VirgileBoraud/myo/Photos&Vidéos/photo.jpg

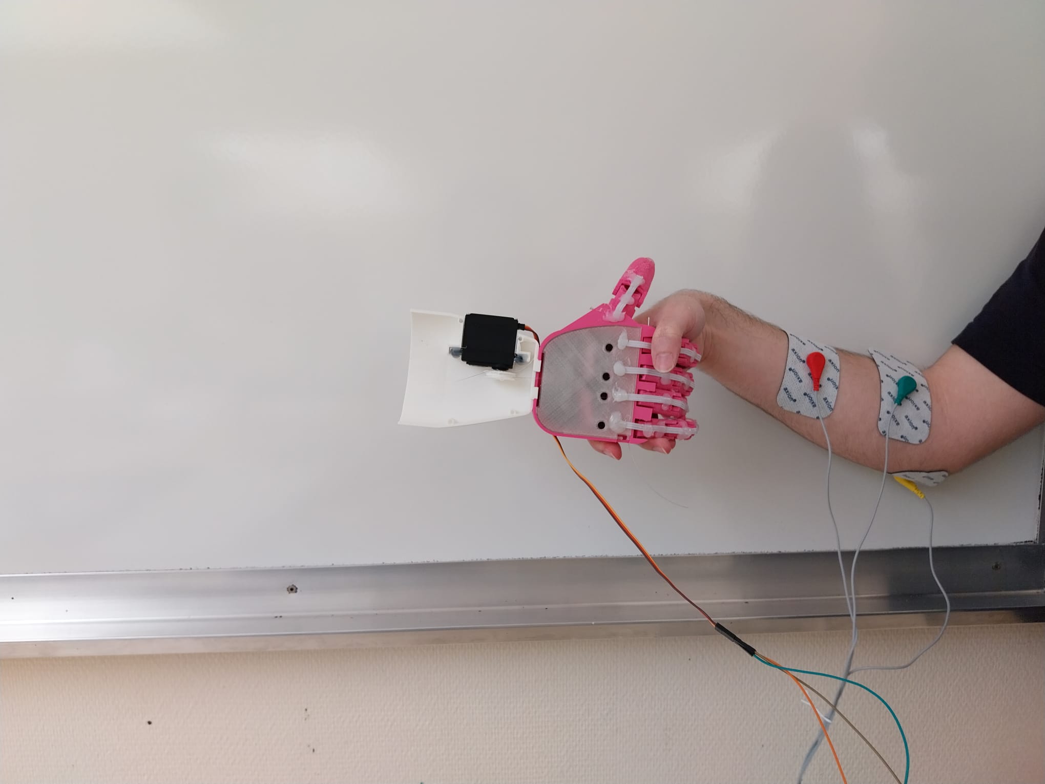
Photos&Vidéos/photo.jpg
