VirgileBoraud/myo/Photos&Vidéos/photo_presentation.jpg

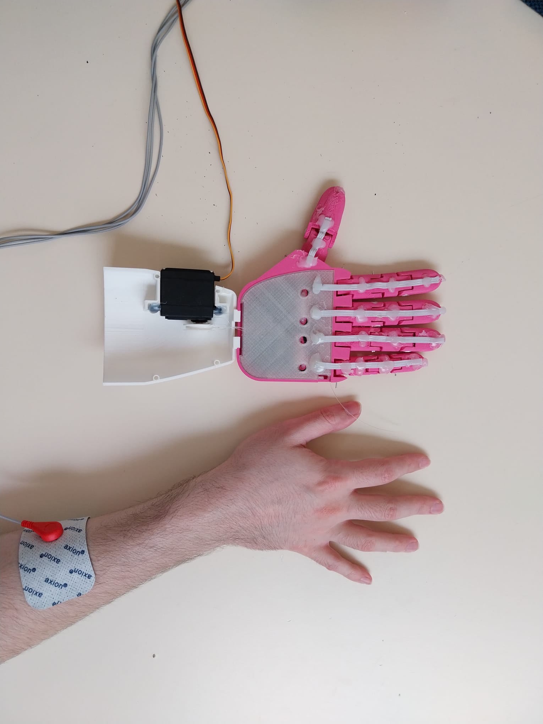
Photos&Vidéos/photo_presentation.jpg
