VirgileBoraud/myo/Programmes/affichage_capteur_EMG/repos.jpg

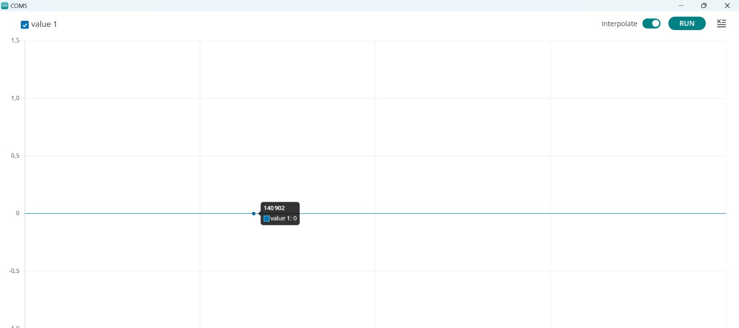
Programmes/affichage_capteur_EMG/repos.jpg
