VirgileBoraud/myo/CAO/Pinky Finger Bottom Proximal.SLDPRT

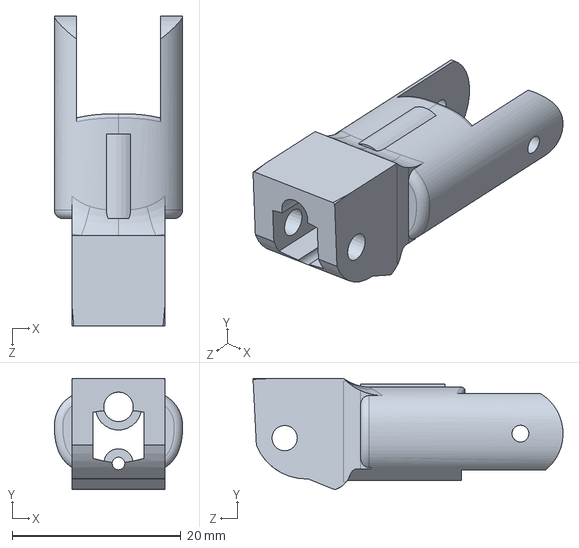
[picture p82: CAD file, 2024-11-13]
CAO/Pinky Finger Bottom Proximal.SLDPRT
15.2 x 13.2 x 36.7 mm
