VirgileBoraud/myo/Photos&Vidéos/montage1.jpg

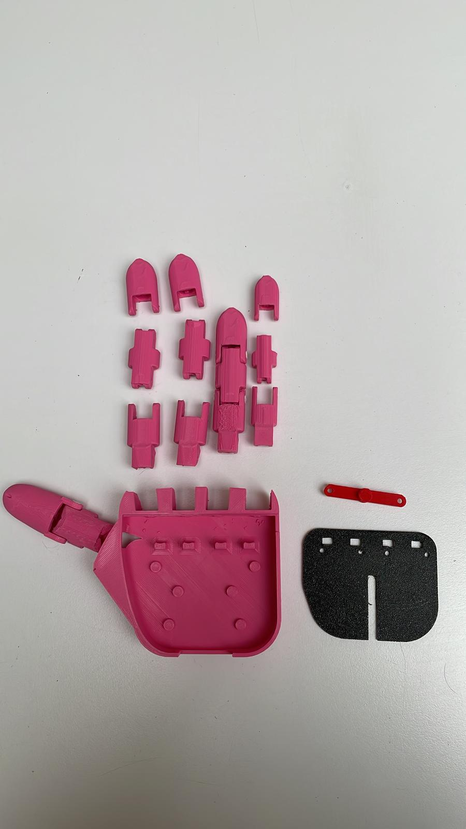
Photos&Vidéos/montage1.jpg
