VirgileBoraud/myo/Photos&Vidéos/montage2.jpg

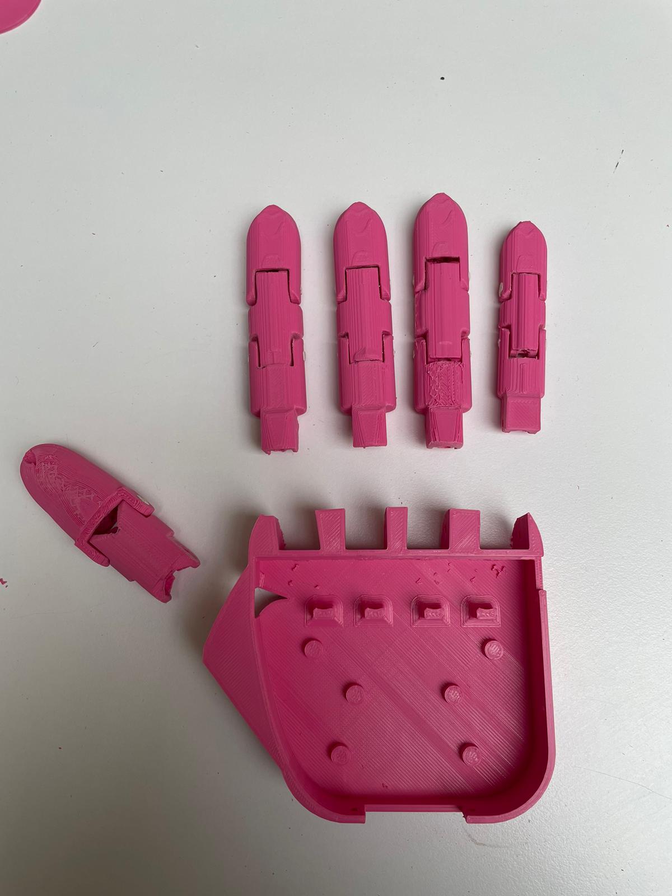
Photos&Vidéos/montage2.jpg
