VirgileBoraud/myo/Photos&Vidéos/montage3.jpg

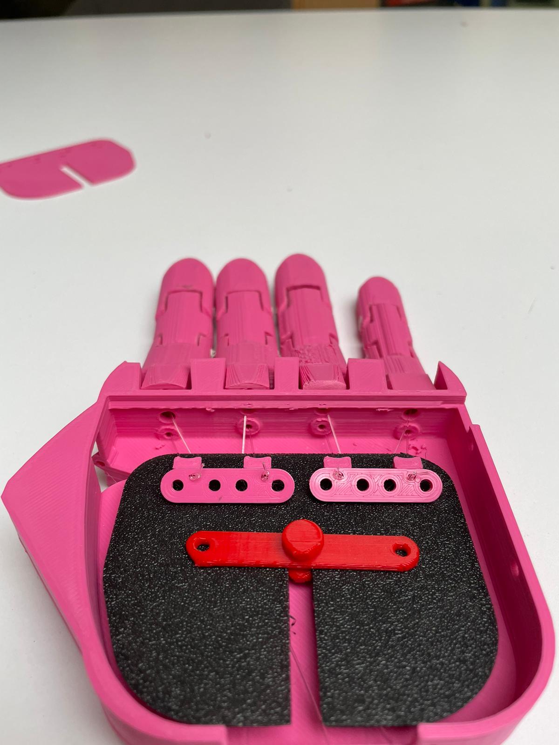
Photos&Vidéos/montage3.jpg
