VirgileBoraud/myo/Photos&Vidéos/montage4.jpg

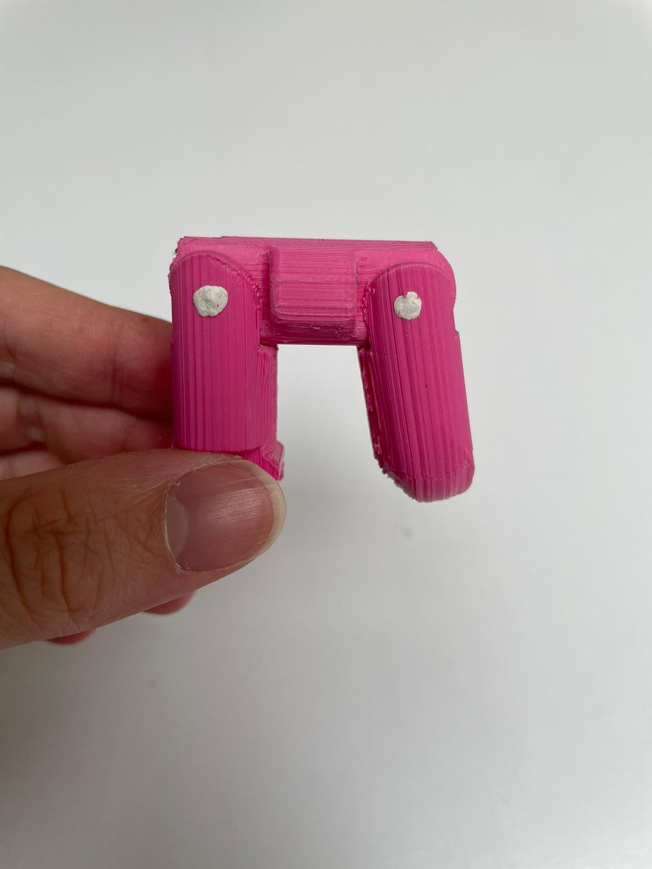
Photos&Vidéos/montage4.jpg
