VirgileBoraud/myo/Photos&Vidéos/montage7.jpg

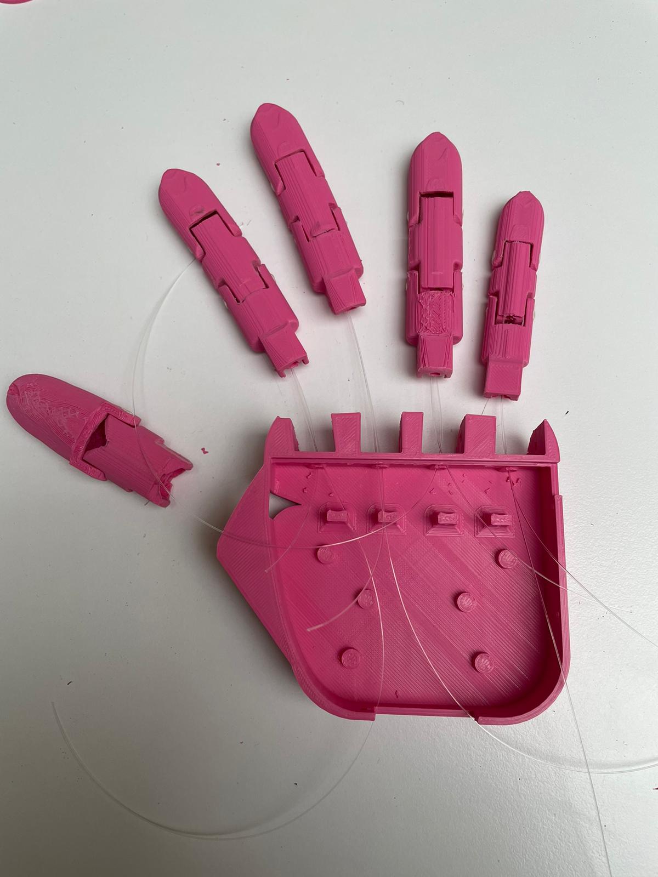
Photos&Vidéos/montage7.jpg
