VirgileBoraud/myo/Photos&Vidéos/montage8.jpg

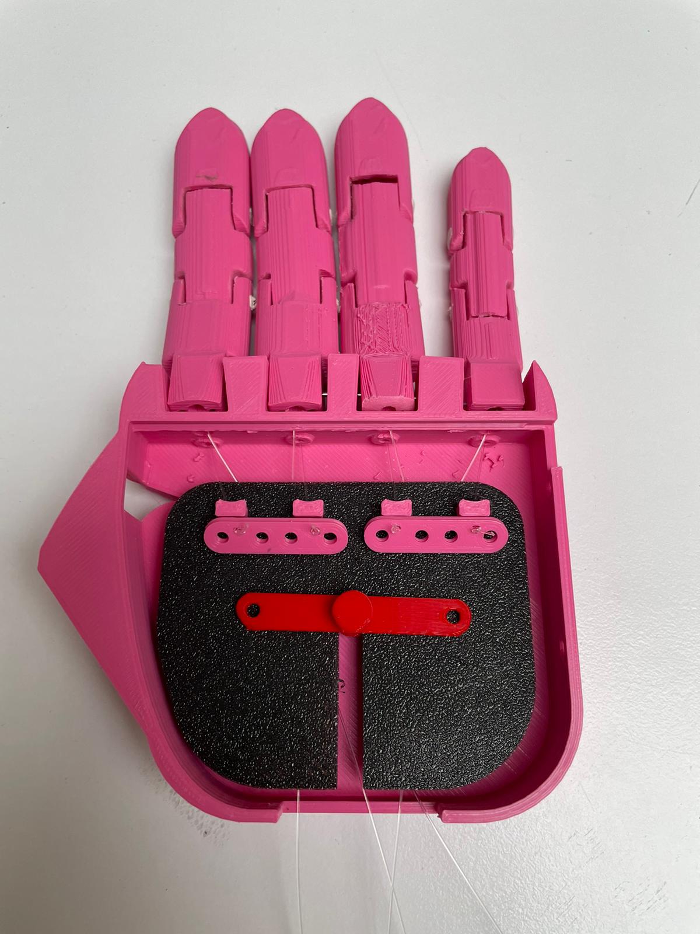
Photos&Vidéos/montage8.jpg
