VirgileBoraud/myo/Photos&Vidéos/montage9.jpg

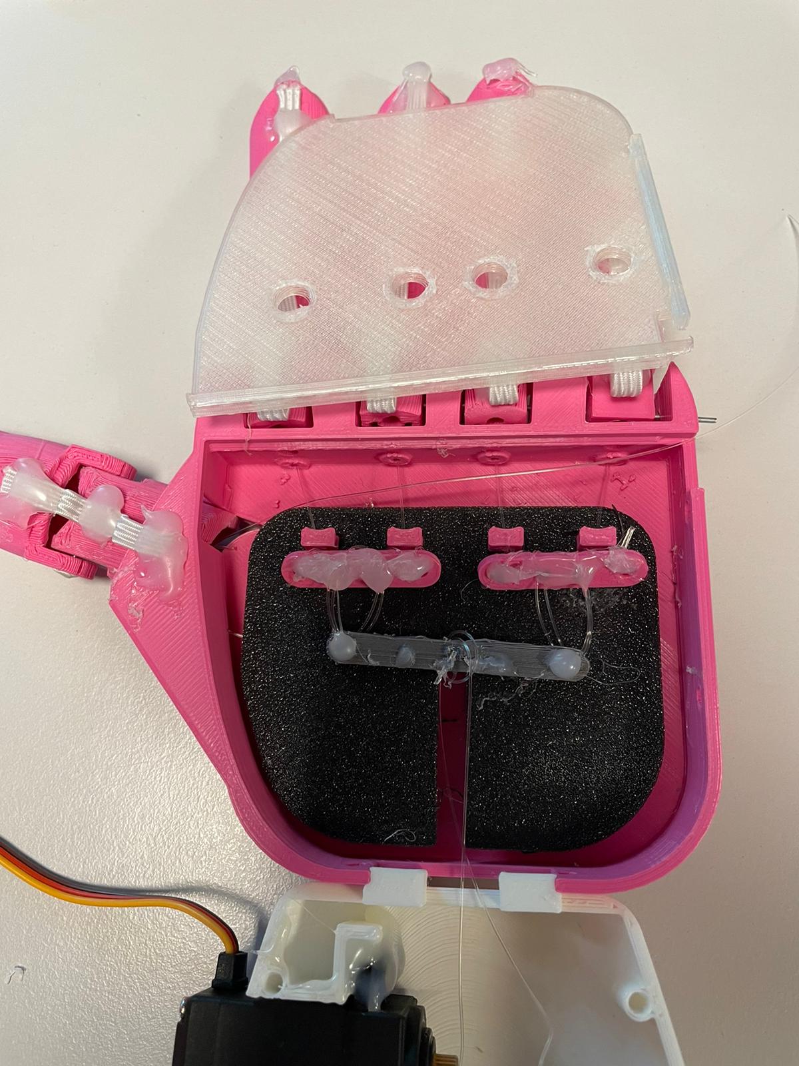
Photos&Vidéos/montage9.jpg
