VirgileBoraud/myo/Photos&Vidéos/montage10.png

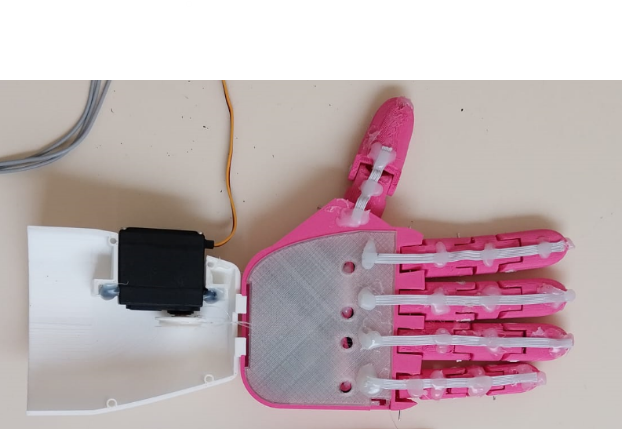
Photos&Vidéos/montage10.png
